MS71/ROSZumo/hw/zumo_tb_01_t.pdf

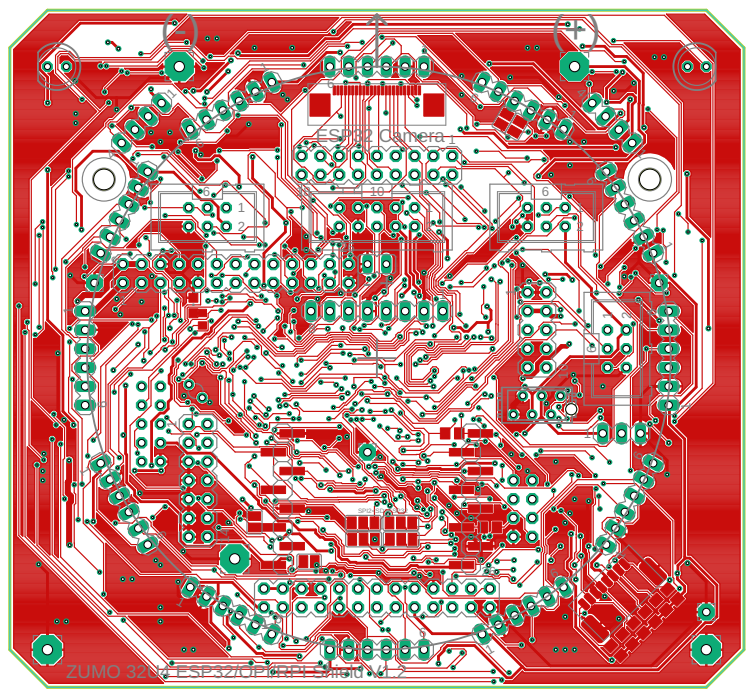
[picture p13: page 1]

ZUMO 32U4 ESP32/OPI/RPI Shield V1.2
