MS71/ROSZumo/hw/zumo_tb_01_sch.pdf

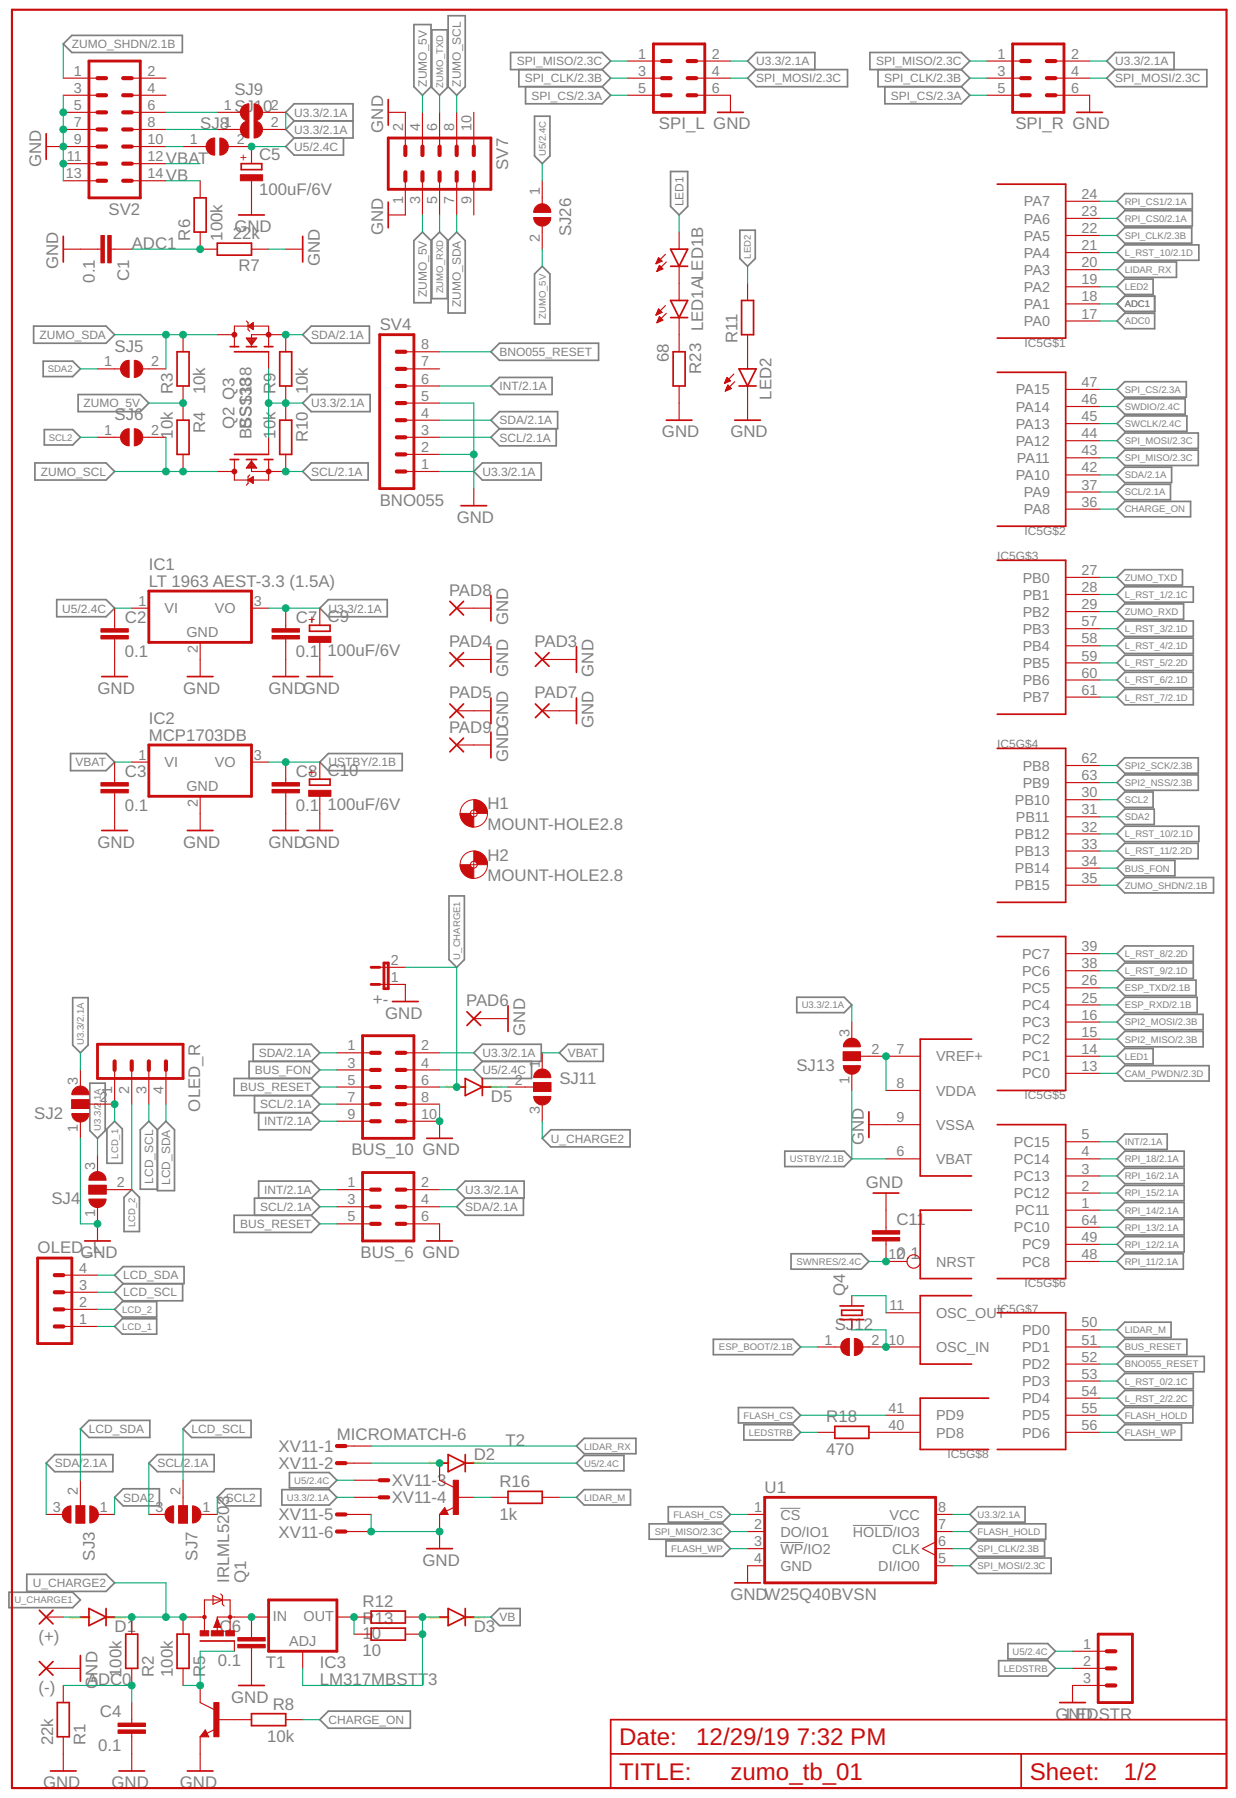
[picture p15: page 1]

GND GND

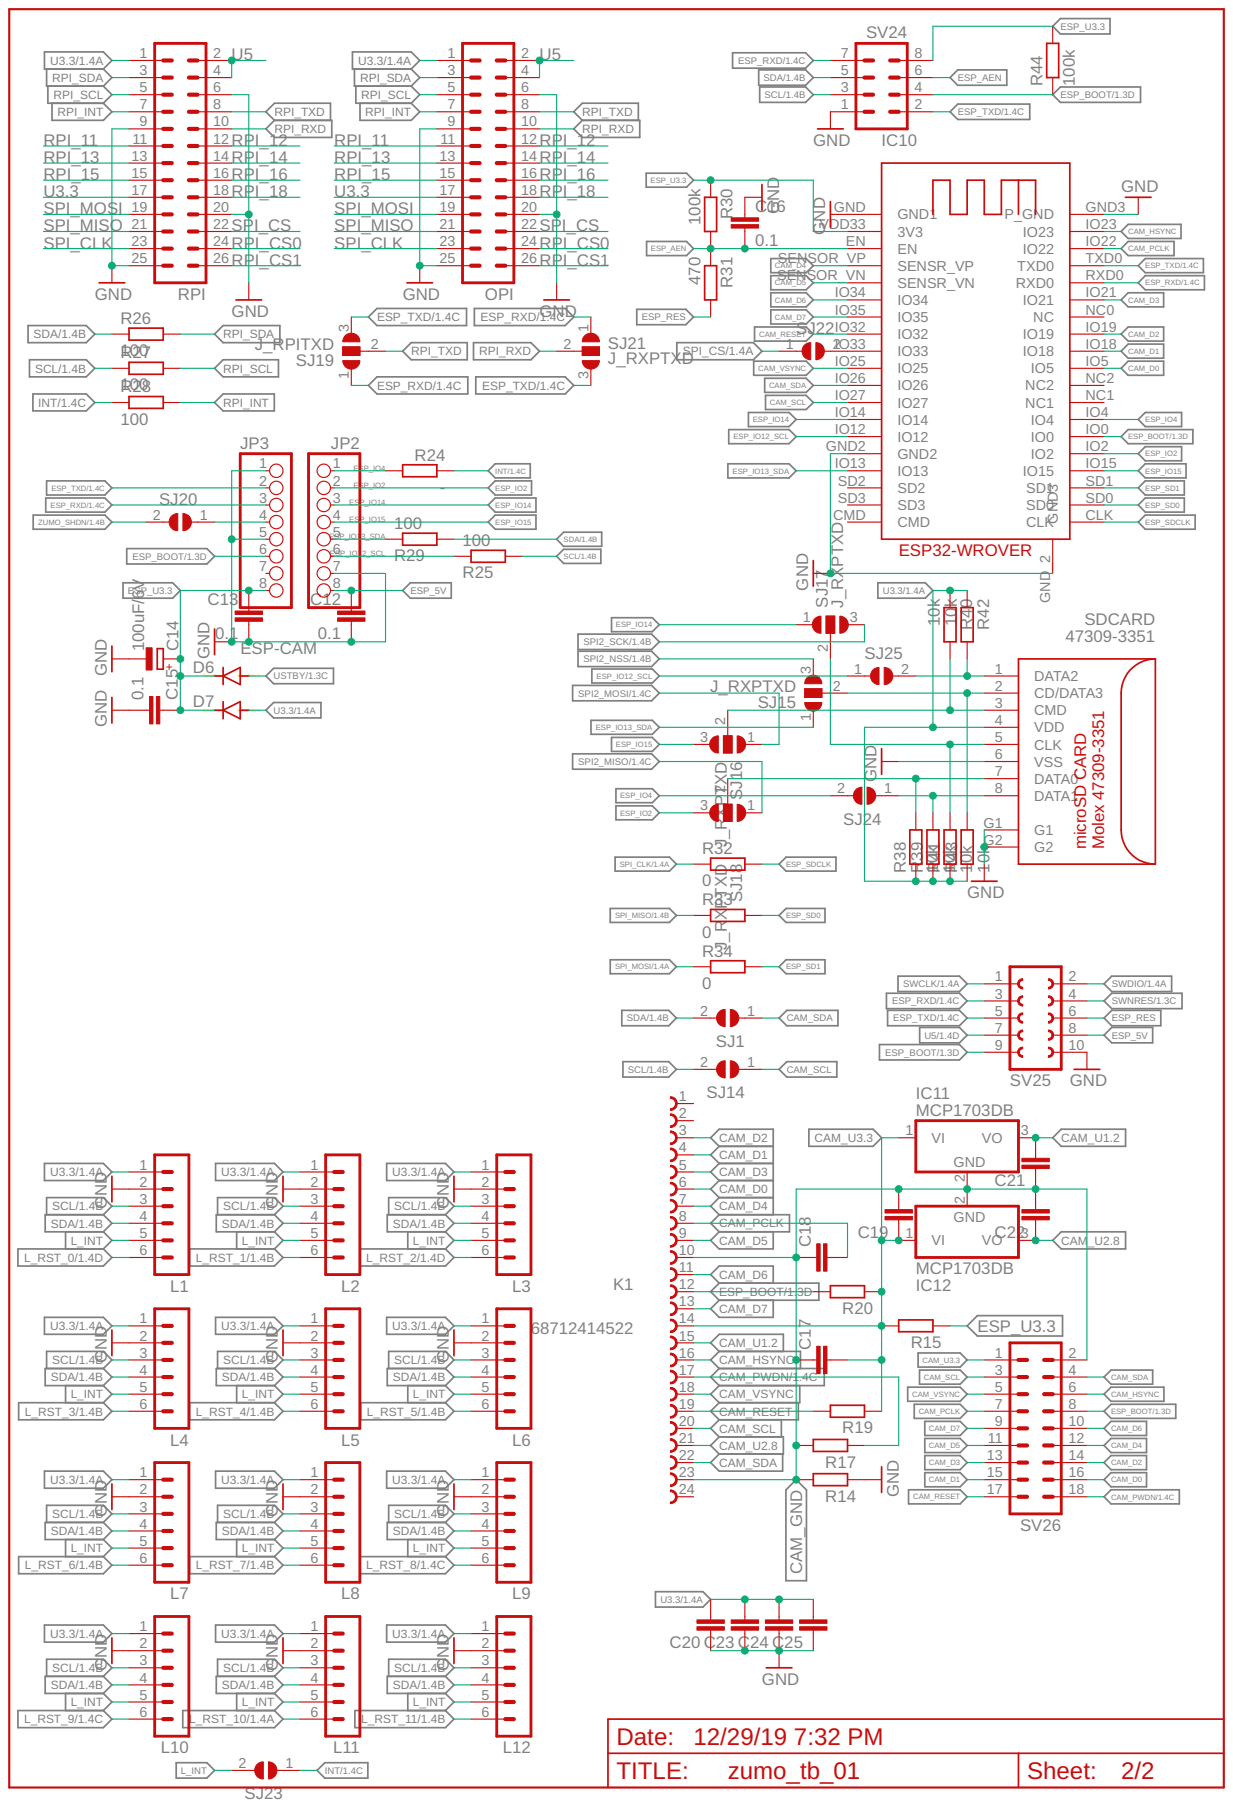
[picture p16: page 2]

SWCLK/1.4A | SWDIO/1.4A
ESP_RXD/1.4C | SWNRES/1.3C
