MS71/ROSZumo/hw/zumo_tb_01.pdf

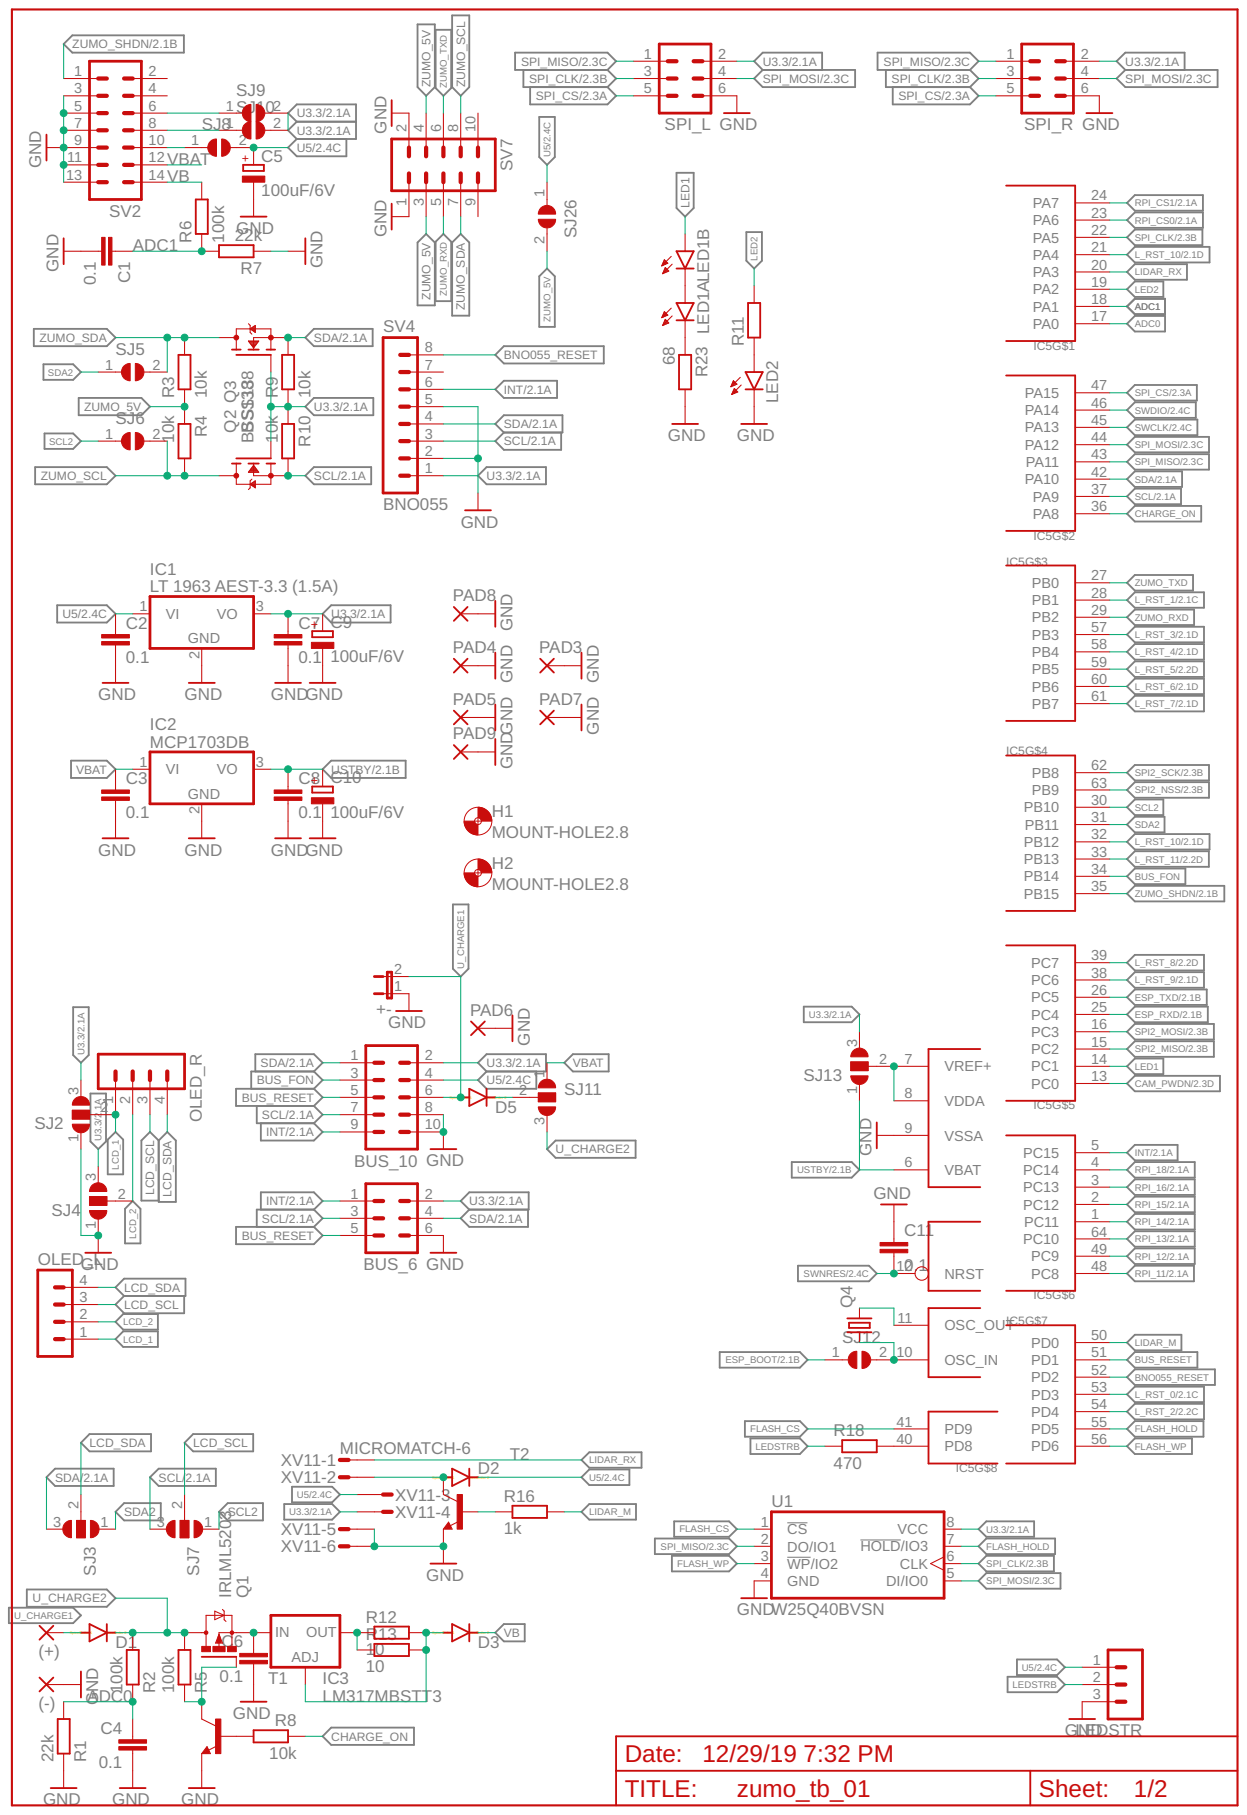
[picture p23: page 1]

11 | 12 VBAT
13 | 14 VB
