MS71/ROSZumo/hw/zumo_tb_01_b.pdf

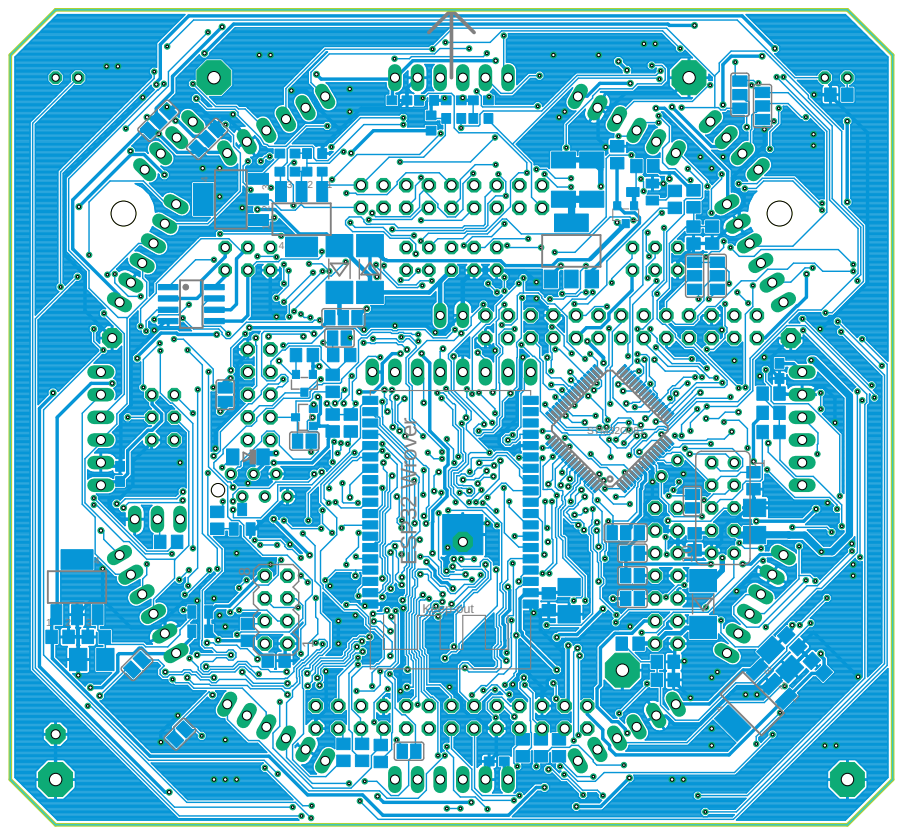
[picture p24: page 1]
