MS71/ROSZumo/hw/zumo_tb_01_bp.pdf

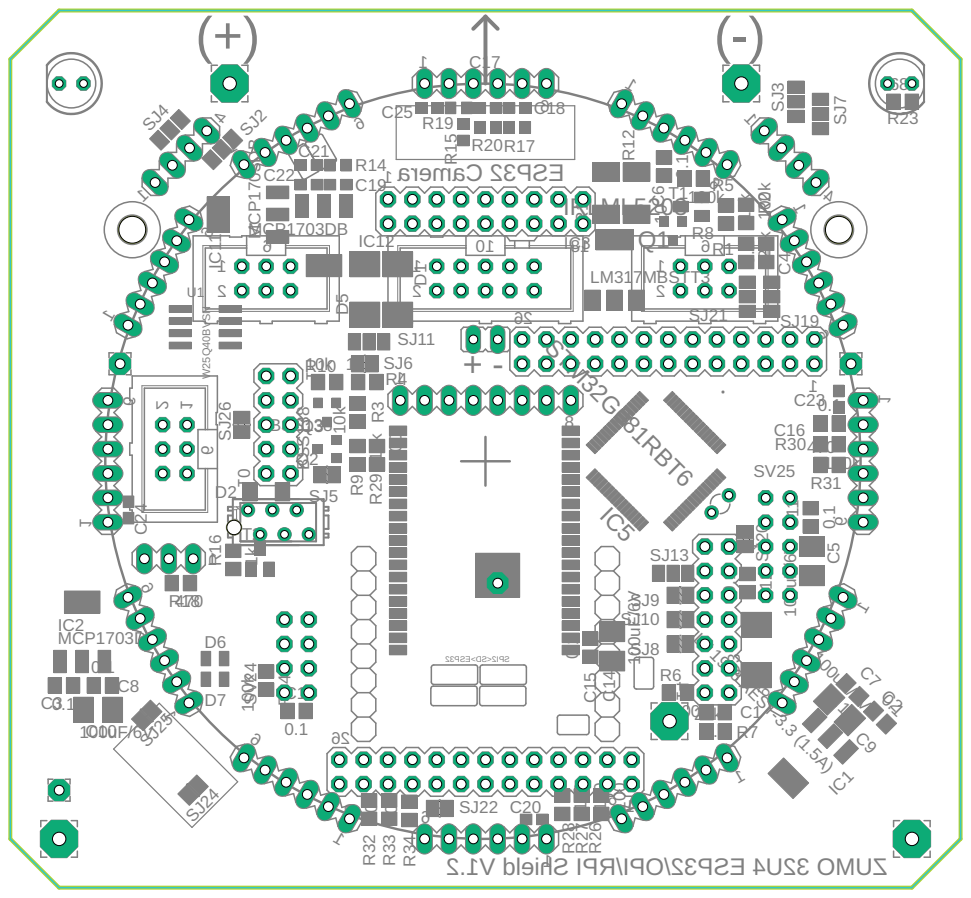
[picture p25: page 1]
