MS71/ROSZumo/fw/stm32/zumo_tb/Drivers/ILI9341/ILI9341_GFX.c

//	MIT License
//
//	Copyright (c) 2017 Matej Artnak
//
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
//
//
//-----------------------------------
//	ILI9341 GFX library for STM32
//-----------------------------------
//
//	Very simple GFX library built upon ILI9342_STM32_Driver library.
//	Adds basic shapes, image and font drawing capabilities to ILI9341
//
//	Library is written for STM32 HAL library and supports STM32CUBEMX. To use the library with Cube software
//	you need to tick the box that generates peripheral initialization code in their own respective .c and .h file
//
//
//-----------------------------------
//	How to use this library
//-----------------------------------
//
//	-If using MCUs other than STM32F7 you will have to change the #include "stm32f7xx_hal.h" in the ILI9341_GFX.h to your respective .h file
//
//	If using "ILI9341_STM32_Driver" then all other prequisites to use the library have allready been met
//	Simply include the library and it is ready to be used
//
//-----------------------------------

#include "ILI9341_STM32_Driver.h"
#include "ILI9341_GFX.h"
#include "5x5_font.h"
#include "spi.h"
#include "main.h"

/*Draw hollow circle at X,Y location with specified radius and colour. X and Y represent circles center */
void ILI9341_Draw_Hollow_Circle(uint16_t X, uint16_t Y, uint16_t Radius, uint16_t Colour)
{
	int x = Radius-1;
    int y = 0;
    int dx = 1;
    int dy = 1;
    int err = dx - (Radius << 1);

    while (x >= y)
    {
        ILI9341_Draw_Pixel(X + x, Y + y, Colour);
        ILI9341_Draw_Pixel(X + y, Y + x, Colour);
        ILI9341_Draw_Pixel(X - y, Y + x, Colour);
        ILI9341_Draw_Pixel(X - x, Y + y, Colour);
        ILI9341_Draw_Pixel(X - x, Y - y, Colour);
        ILI9341_Draw_Pixel(X - y, Y - x, Colour);
        ILI9341_Draw_Pixel(X + y, Y - x, Colour);
        ILI9341_Draw_Pixel(X + x, Y - y, Colour);

        if (err <= 0)
        {
            y++;
            err += dy;
            dy += 2;
        }
        if (err > 0)
        {
            x--;
            dx += 2;
            err += (-Radius << 1) + dx;
        }
    }
}

/*Draw filled circle at X,Y location with specified radius and colour. X and Y represent circles center */
void ILI9341_Draw_Filled_Circle(uint16_t X, uint16_t Y, uint16_t Radius, uint16_t Colour)
{
	
		int x = Radius;
    int y = 0;
    int xChange = 1 - (Radius << 1);
    int yChange = 0;
    int radiusError = 0;

    while (x >= y)
    {
        for (int i = X - x; i <= X + x; i++)
        {
            ILI9341_Draw_Pixel(i, Y + y,Colour);
            ILI9341_Draw_Pixel(i, Y - y,Colour);
        }
        for (int i = X - y; i <= X + y; i++)
        {
            ILI9341_Draw_Pixel(i, Y + x,Colour);
            ILI9341_Draw_Pixel(i, Y - x,Colour);
        }

        y++;
        radiusError += yChange;
        yChange += 2;
        if (((radiusError << 1) + xChange) > 0)
        {
            x--;
            radiusError += xChange;
            xChange += 2;
        }
    }
		//Really slow implementation, will require future overhaul
		//TODO:	https://stackoverflow.com/questions/1201200/fast-algorithm-for-drawing-filled-circles	
}

/*Draw a hollow rectangle between positions X0,Y0 and X1,Y1 with specified colour*/
void ILI9341_Draw_Hollow_Rectangle_Coord(uint16_t X0, uint16_t Y0, uint16_t X1, uint16_t Y1, uint16_t Colour)
{
	uint16_t 	X_length = 0;
	uint16_t 	Y_length = 0;
	uint8_t		Negative_X = 0;
	uint8_t 	Negative_Y = 0;
	float 		Calc_Negative = 0;
	
	Calc_Negative = X1 - X0;
	if(Calc_Negative < 0) Negative_X = 1;
	Calc_Negative = 0;
	
	Calc_Negative = Y1 - Y0;
	if(Calc_Negative < 0) Negative_Y = 1;
	
	
	//DRAW HORIZONTAL!
	if(!Negative_X)
	{
		X_length = X1 - X0;		
	}
	else
	{
		X_length = X0 - X1;		
	}
	ILI9341_Draw_Horizontal_Line(X0, Y0, X_length, Colour);
	ILI9341_Draw_Horizontal_Line(X0, Y1, X_length, Colour);
	
	
	
	//DRAW VERTICAL!
	if(!Negative_Y)
	{
		Y_length = Y1 - Y0;		
	}
	else
	{
		Y_length = Y0 - Y1;		
	}
	ILI9341_Draw_Vertical_Line(X0, Y0, Y_length, Colour);
	ILI9341_Draw_Vertical_Line(X1, Y0, Y_length, Colour);
	
	if((X_length > 0)||(Y_length > 0)) 
	{
		ILI9341_Draw_Pixel(X1, Y1, Colour);
	}
	
}

/*Draw a filled rectangle between positions X0,Y0 and X1,Y1 with specified colour*/
void ILI9341_Draw_Filled_Rectangle_Coord(uint16_t X0, uint16_t Y0, uint16_t X1, uint16_t Y1, uint16_t Colour)
{
	uint16_t 	X_length = 0;
	uint16_t 	Y_length = 0;
	uint8_t		Negative_X = 0;
	uint8_t 	Negative_Y = 0;
	int32_t 	Calc_Negative = 0;
	
	uint16_t X0_true = 0;
	uint16_t Y0_true = 0;
	
	Calc_Negative = X1 - X0;
	if(Calc_Negative < 0) Negative_X = 1;
	Calc_Negative = 0;
	
	Calc_Negative = Y1 - Y0;
	if(Calc_Negative < 0) Negative_Y = 1;
	
	
	//DRAW HORIZONTAL!
	if(!Negative_X)
	{
		X_length = X1 - X0;
		X0_true = X0;
	}
	else
	{
		X_length = X0 - X1;
		X0_true = X1;
	}
	
	//DRAW VERTICAL!
	if(!Negative_Y)
	{
		Y_length = Y1 - Y0;
		Y0_true = Y0;		
	}
	else
	{
		Y_length = Y0 - Y1;
		Y0_true = Y1;	
	}
	
	ILI9341_Draw_Rectangle(X0_true, Y0_true, X_length, Y_length, Colour);	
}

/*Draws a character (fonts imported from fonts.h) at X,Y location with specified font colour, size and Background colour*/
/*See fonts.h implementation of font on what is required for changing to a different font when switching fonts libraries*/
void ILI9341_Draw_Char(char Character, uint16_t X, uint16_t Y, uint16_t Colour, uint16_t Size, uint16_t Background_Colour)
{
	uint8_t 	function_char;
	uint16_t 	i,j;

	function_char = Character;

	if (function_char < ' ') {
		Character = 0;
	} else {
		function_char -= 32;
	}

	char temp[CHAR_WIDTH];
	for(uint8_t k = 0; k<CHAR_WIDTH; k++)
	{
		temp[k] = font[function_char][k];
	}

	// Draw pixels
	ILI9341_Draw_Rectangle(X, Y, CHAR_WIDTH*Size, CHAR_HEIGHT*Size, Background_Colour);
	for (j=0; j<CHAR_WIDTH; j++) {
		for (i=0; i<CHAR_HEIGHT; i++) {
			if (temp[j] & (1<<i)) {
				if(Size == 1)
				{
					ILI9341_Draw_Pixel(X+j, Y+i, Colour);
				}
				else
				{
					ILI9341_Draw_Rectangle(X+(j*Size), Y+(i*Size), Size, Size, Colour);
				}
			}
		}
	}
}

/*Draws an array of characters (fonts imported from fonts.h) at X,Y location with specified font colour, size and Background colour*/
/*See fonts.h implementation of font on what is required for changing to a different font when switching fonts libraries*/
void ILI9341_Draw_Text(const char* Text, uint16_t X, uint16_t Y, uint16_t Colour, uint16_t Size, uint16_t Background_Colour)
{
    while (*Text) {
        ILI9341_Draw_Char(*Text++, X, Y, Colour, Size, Background_Colour);
        X += CHAR_WIDTH*Size;
    }
}

/*Draws a full screen picture from flash. Image converted from RGB .jpeg/other to C array using online converter*/
//USING CONVERTER: http://www.digole.com/tools/PicturetoC_Hex_converter.php
//65K colour (2Bytes / Pixel)
void ILI9341_Draw_Image(const char* Image_Array, uint8_t Orientation)
{
	if(Orientation == SCREEN_HORIZONTAL_1)
	{
		ILI9341_Set_Rotation(SCREEN_HORIZONTAL_1);
		ILI9341_Set_Address(0,0,ILI9341_SCREEN_WIDTH,ILI9341_SCREEN_HEIGHT);
			
		HAL_GPIO_WritePin(LCD_DC_Port, LCD_DC_PIN, GPIO_PIN_SET);
		HAL_GPIO_WritePin(LCD_CS_Port, LCD_CS_PIN, GPIO_PIN_RESET);
		
		unsigned char Temp_small_buffer[BURST_MAX_SIZE];
		uint32_t counter = 0;
		for(uint32_t i = 0; i < ILI9341_SCREEN_WIDTH*ILI9341_SCREEN_HEIGHT*2/BURST_MAX_SIZE; i++)
		{			
				for(uint32_t k = 0; k< BURST_MAX_SIZE; k++)
				{
					Temp_small_buffer[k]	= Image_Array[counter+k];		
				}						
				HAL_SPI_Transmit(&hspi1, (unsigned char*)Temp_small_buffer, BURST_MAX_SIZE, 10);
				counter += BURST_MAX_SIZE;			
		}
		HAL_GPIO_WritePin(LCD_CS_Port, LCD_CS_PIN, GPIO_PIN_SET);
	}
	else if(Orientation == SCREEN_HORIZONTAL_2)
	{
		ILI9341_Set_Rotation(SCREEN_HORIZONTAL_2);
		ILI9341_Set_Address(0,0,ILI9341_SCREEN_WIDTH,ILI9341_SCREEN_HEIGHT);
			
		HAL_GPIO_WritePin(LCD_DC_Port, LCD_DC_PIN, GPIO_PIN_SET);
		HAL_GPIO_WritePin(LCD_CS_Port, LCD_CS_PIN, GPIO_PIN_RESET);
		
		unsigned char Temp_small_buffer[BURST_MAX_SIZE];
		uint32_t counter = 0;
		for(uint32_t i = 0; i < ILI9341_SCREEN_WIDTH*ILI9341_SCREEN_HEIGHT*2/BURST_MAX_SIZE; i++)
		{			
				for(uint32_t k = 0; k< BURST_MAX_SIZE; k++)
				{
					Temp_small_buffer[k]	= Image_Array[counter+k];		
				}						
				HAL_SPI_Transmit(&hspi1, (unsigned char*)Temp_small_buffer, BURST_MAX_SIZE, 10);
				counter += BURST_MAX_SIZE;			
		}
		HAL_GPIO_WritePin(LCD_CS_Port, LCD_CS_PIN, GPIO_PIN_SET);
	}
	else if(Orientation == SCREEN_VERTICAL_2)
	{
		ILI9341_Set_Rotation(SCREEN_VERTICAL_2);
		ILI9341_Set_Address(0,0,ILI9341_SCREEN_HEIGHT,ILI9341_SCREEN_WIDTH);
			
		HAL_GPIO_WritePin(LCD_DC_Port, LCD_DC_PIN, GPIO_PIN_SET);
		HAL_GPIO_WritePin(LCD_CS_Port, LCD_CS_PIN, GPIO_PIN_RESET);
		
		unsigned char Temp_small_buffer[BURST_MAX_SIZE];
		uint32_t counter = 0;
		for(uint32_t i = 0; i < ILI9341_SCREEN_WIDTH*ILI9341_SCREEN_HEIGHT*2/BURST_MAX_SIZE; i++)
		{			
				for(uint32_t k = 0; k< BURST_MAX_SIZE; k++)
				{
					Temp_small_buffer[k]	= Image_Array[counter+k];		
				}						
				HAL_SPI_Transmit(&hspi1, (unsigned char*)Temp_small_buffer, BURST_MAX_SIZE, 10);
				counter += BURST_MAX_SIZE;			
		}
		HAL_GPIO_WritePin(LCD_CS_Port, LCD_CS_PIN, GPIO_PIN_SET);
	}
	else if(Orientation == SCREEN_VERTICAL_1)
	{
		ILI9341_Set_Rotation(SCREEN_VERTICAL_1);
		ILI9341_Set_Address(0,0,ILI9341_SCREEN_HEIGHT,ILI9341_SCREEN_WIDTH);
			
		HAL_GPIO_WritePin(LCD_DC_Port, LCD_DC_PIN, GPIO_PIN_SET);
		HAL_GPIO_WritePin(LCD_CS_Port, LCD_CS_PIN, GPIO_PIN_RESET);
		
		unsigned char Temp_small_buffer[BURST_MAX_SIZE];
		uint32_t counter = 0;
		for(uint32_t i = 0; i < ILI9341_SCREEN_WIDTH*ILI9341_SCREEN_HEIGHT*2/BURST_MAX_SIZE; i++)
		{			
				for(uint32_t k = 0; k< BURST_MAX_SIZE; k++)
				{
					Temp_small_buffer[k]	= Image_Array[counter+k];		
				}						
				HAL_SPI_Transmit(&hspi1, (unsigned char*)Temp_small_buffer, BURST_MAX_SIZE, 10);
				counter += BURST_MAX_SIZE;			
		}
		HAL_GPIO_WritePin(LCD_CS_Port, LCD_CS_PIN, GPIO_PIN_SET);
	}
}
