MS71/ROSZumo/fw/stm32/zumo_tb/Core/Inc/config.h

#ifndef _CONFIG_H_
#define _CONFIG_H_

//#define ENABLE_SEMI_PRINTF
//#define ENABLE_STANDBY
#ifdef ENABLE_SEMI_PRINTF
#define ENABLE_PM_PRINTF
#endif
//#define ENABLE_LCD_UI
#define ENABLE_IRQ_ADC

#endif
